BilginistAdam/esp32-led-controller/hardware/scripts/placement.py

# ref: (x, y, rotation_deg, side)
BOARD = (100, 100, 164, 138, 2.0)   # x0,y0,x1,y1, corner radius
PLACE = {
    "J1": (105.0, 104.5, 270, "F"),
    "J2": (105.0, 122.0, 270, "F"),
    "F1": (115.5, 103.5, 0, "F"),
    "D3": (115.5, 107.5, 0, "F"),
    "D1": (115.5, 111.5, 0, "F"),
    "D2": (125.0, 124.0, 0, "F"),
    "C1": (121.0, 108.0, 90, "F"),
    "C2": (123.5, 108.0, 90, "F"),
    "U1": (127.5, 108.0, 0, "F"),
    "C3": (127.5, 104.5, 0, "F"),
    "L1": (132.5, 108.0, 0, "F"),
    "C4": (137.0, 108.0, 90, "F"),
    "C5": (139.5, 108.0, 90, "F"),
    "J4": (144.0, 102.5, 90, "F"),
    "U2": (156.8, 120.0, 270, "F"),
    "C6": (161.0, 107.6, 0, "F"),
    "C7": (157.5, 107.6, 0, "F"),
    "R1": (154.0, 107.6, 0, "F"),
    "C8": (150.5, 107.6, 0, "F"),
    "R2": (147.5, 110.0, 0, "F"),
    "R3": (147.5, 112.5, 0, "F"),
    "R4": (153.5, 132.0, 0, "F"),
    "J3": (130.0, 134.2, 0, "F"),
    "R8": (122.5, 131.0, 90, "F"),
    "R9": (137.0, 131.0, 90, "F"),
    "SW1": (115.0, 133.5, 0, "F"),
    "SW2": (142.5, 133.5, 0, "F"),
    "Q1": (113.0, 124.0, 0, "F"),
    "R5": (120.0, 121.5, 0, "F"),
    "R6": (117.5, 127.0, 0, "F"),
    "D4": (149.5, 134.6, 0, "F"),
    "R7": (149.5, 132.0, 0, "F"),
}
HOLES = [(159.0, 103.0), (159.0, 134.5), (104.0, 134.6), (114.5, 116.8)]
SILK = [
    ("+", 101.3, 104.5, 1.4), ("-", 101.3, 109.6, 1.4),
    ("+", 101.3, 122.0, 1.4), ("-", 101.3, 127.1, 1.4),
]
